nathanshaw/Legatus/PCB/legacy/audio_codec_breakouts/ws8731_audio_codec/panel/ws8731_breakout_panel.brd

## EAGLE design PCB/legacy/audio_codec_breakouts/ws8731_audio_codec/panel/ws8731_breakout_panel.brd (2022-09-17, an earlier design)

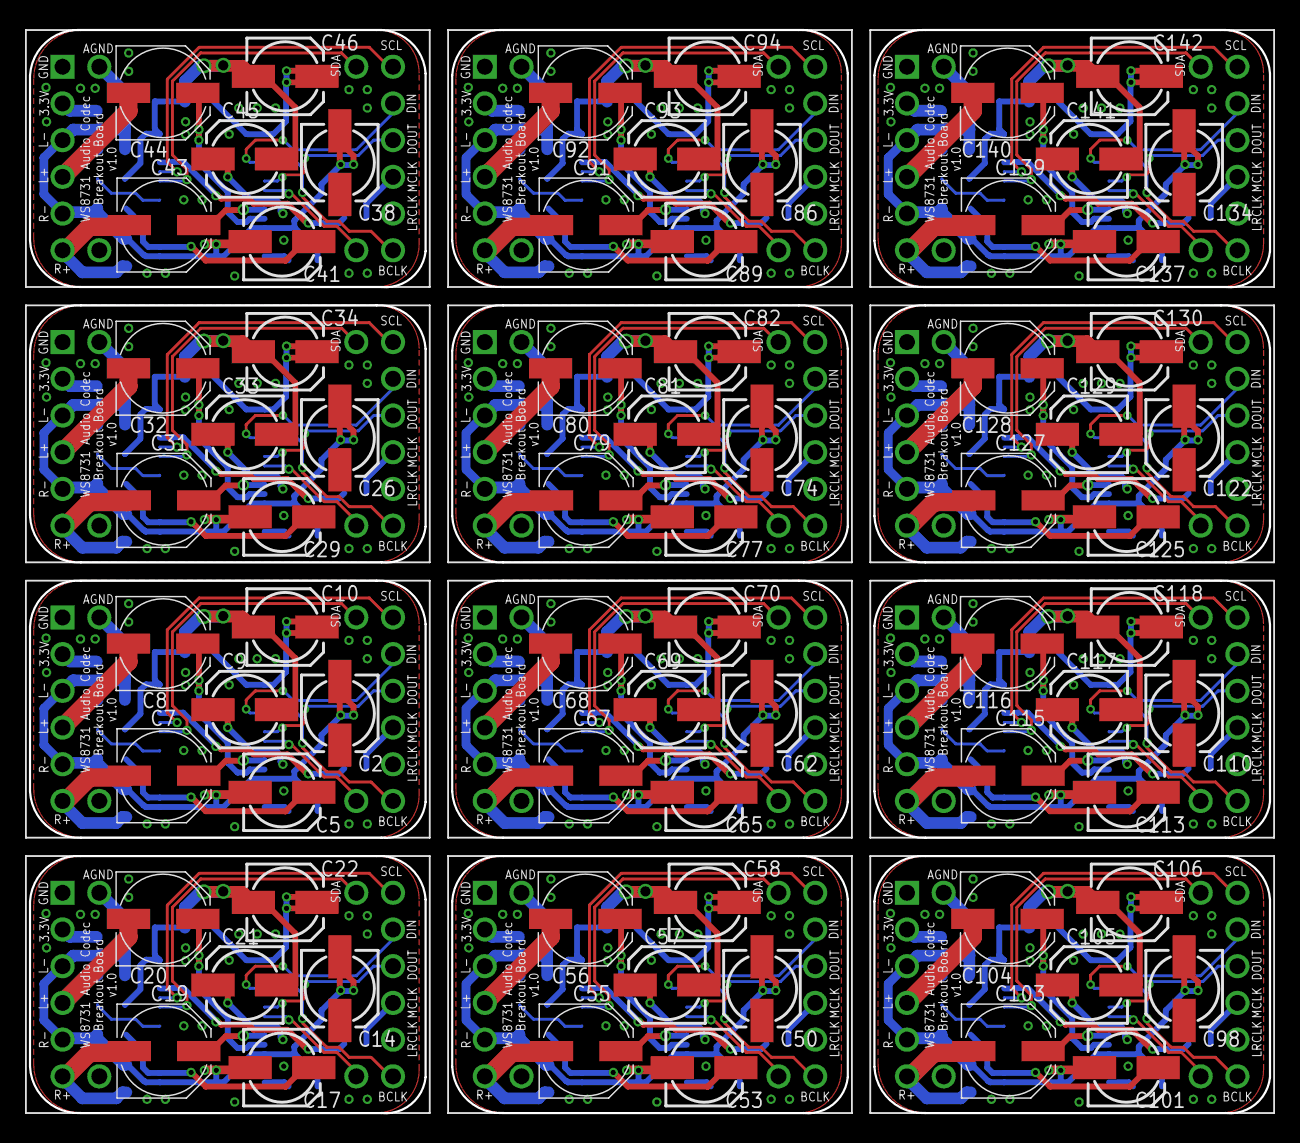
[picture p24: board ws8731_breakout_panel.brd from above]

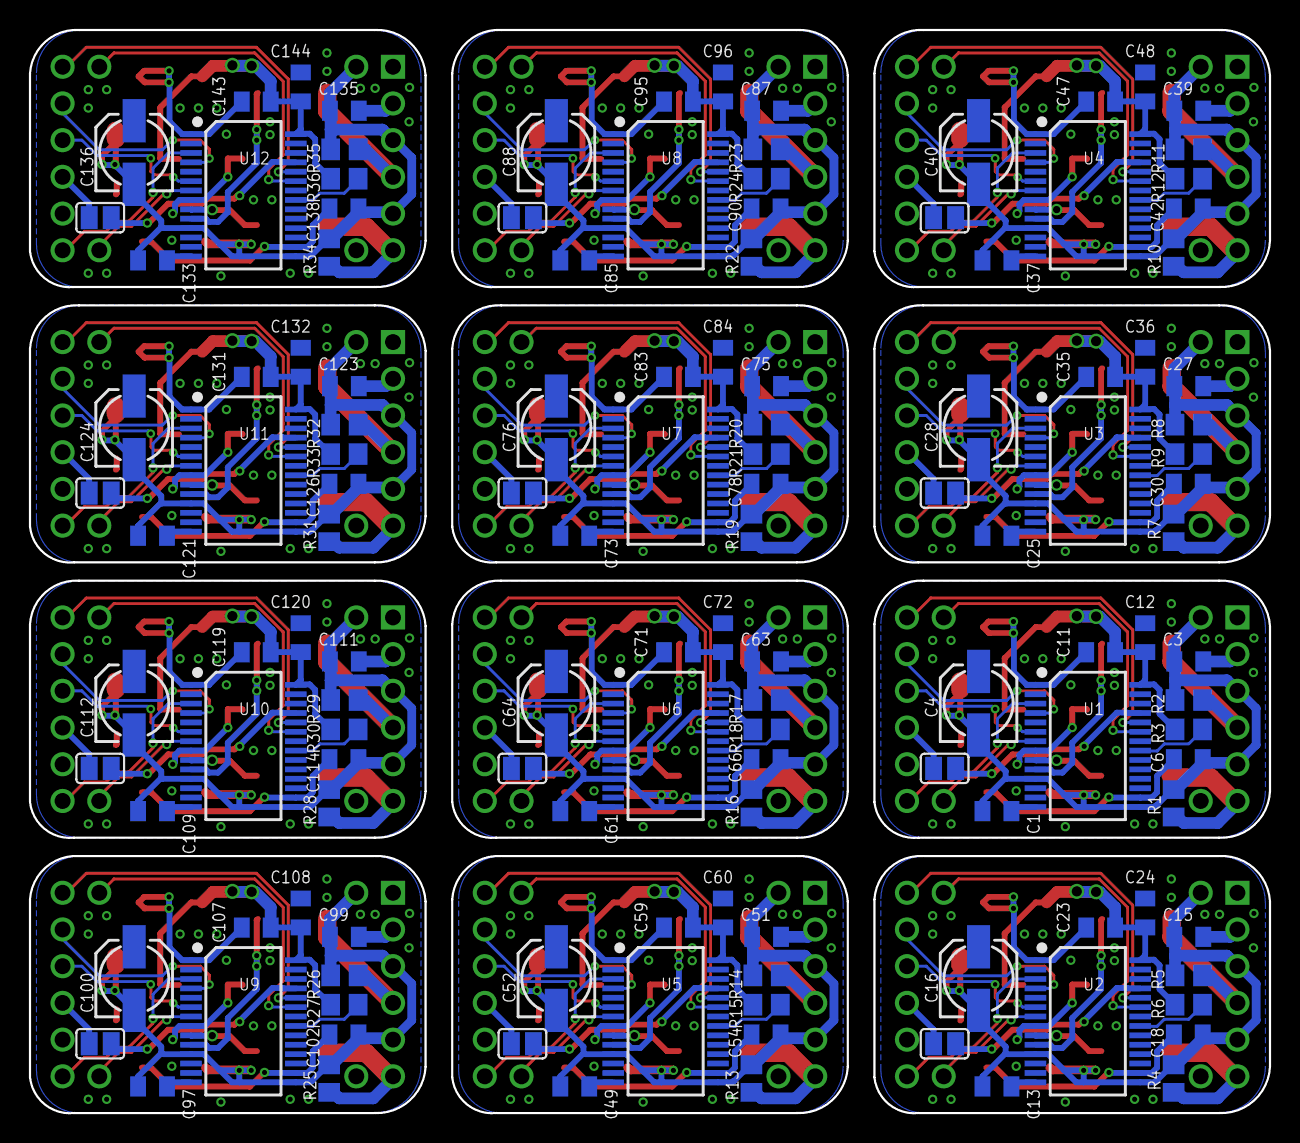
[picture p25: board ws8731_breakout_panel.brd from below]

Board: 2 copper layers, 85.8 x 74.9 mm, 216 parts (132 on the bottom side), 216 nets.

Parts:
C1, C3, C6, C11, C12, C13, C15, C18, C23, C24, C25, C27, C30, C35, C36, C37, C39, C42, C47, C48, C49, C51, C54, C59, C60, C61, C63, C66, C71, C72, C73, C75, C78, C83, C84, C85, C87, C90, C95, C96, C97, C99, C102, C107, C108, C109, C111, C114, C119, C120, C121, C123, C126, C131, C132, C133, C135, C138, C143, C144: 0.1uf; C0805K
C2, C4, C5, C9, C10, C14, C16, C17, C21, C22, C26, C28, C29, C33, C34, C38, C40, C41, C45, C46, C50, C52, C53, C57, C58, C62, C64, C65, C69, C70, C74, C76, C77, C81, C82, C86, C88, C89, C93, C94, C98, C100, C101, C105, C106, C110, C112, C113, C117, C118, C122, C124, C125, C129, C130, C134, C136, C137, C141, C142: 10uf; 153CLV-0505
C7, C8, C19, C20, C31, C32, C43, C44, C55, C56, C67, C68, C79, C80, C91, C92, C103, C104, C115, C116, C127, C128, C139, C140: 220uf; PANASONIC_D
R1, R2, R4, R5, R7, R8, R10, R11, R13, R14, R16, R17, R19, R20, R22, R23, R25, R26, R28, R29, R31, R32, R34, R35: 47k; R0805
R3, R6, R9, R12, R15, R18, R21, R24, R27, R30, R33, R36: 10k; R0805
SJ1, SJ2, SJ3, SJ4, SJ5, SJ6, SJ7, SJ8, SJ9, SJ10, SJ11, SJ12: SJ
U1, U2, U3, U4, U5, U6, U7, U8, U9, U10, U11, U12: CODECODER-WM8731SEDS/V(SSOP28); SSOP28-0.65-10.2X5.2MM
U$1, U$2, U$3, U$4, U$5, U$6, U$7, U$8, U$9, U$10, U$11, U$12: AUDIO_CODEC_BREAKOUT; HSS_CODEC_BREAKOUT

Connections:
3.3V: C13.1, C14.+, C15.1, C16.+, C21.+, C24.1, U2.8, U2.14, U2.27, U$12.3.3
3.3V1: C1.1, C2.+, C3.1, C4.+, C9.+, C12.1, U1.8, U1.14, U1.27, U$1.3.3
3.3V2: C25.1, C26.+, C27.1, C28.+, C33.+, C36.1, U3.8, U3.14, U3.27, U$2.3.3
3.3V3: C37.1, C38.+, C39.1, C40.+, C45.+, C48.1, U4.8, U4.14, U4.27, U$3.3.3
3.3V4: C49.1, C50.+, C51.1, C52.+, C57.+, C60.1, U5.8, U5.14, U5.27, U$4.3.3
3.3V5: C61.1, C62.+, C63.1, C64.+, C69.+, C72.1, U6.8, U6.14, U6.27, U$5.3.3
3.3V6: C73.1, C74.+, C75.1, C76.+, C81.+, C84.1, U7.8, U7.14, U7.27, U$6.3.3
3.3V7: C85.1, C86.+, C87.1, C88.+, C93.+, C96.1, U8.8, U8.14, U8.27, U$7.3.3
3.3V8: C97.1, C98.+, C99.1, C100.+, C105.+, C108.1, U9.8, U9.14, U9.27, U$8.3.3
3.3V9: C109.1, C110.+, C111.1, C112.+, C117.+, C120.1, U10.8, U10.14, U10.27, U$9.3.3
3.3V10: C121.1, C122.+, C123.1, C124.+, C129.+, C132.1, U11.8, U11.14, U11.27, U$10.3.3
3.3V11: C133.1, C134.+, C135.1, C136.+, C141.+, C144.1, U12.8, U12.14, U12.27, U$11.3.3
ADCLRCLK: U2.7, U$12.NA2
ADCLRCLK1: U1.7, U$1.NA2
ADCLRCLK2: U3.7, U$2.NA2
ADCLRCLK3: U4.7, U$3.NA2
ADCLRCLK4: U5.7, U$4.NA2
ADCLRCLK5: U6.7, U$5.NA2
ADCLRCLK6: U7.7, U$6.NA2
ADCLRCLK7: U8.7, U$7.NA2
ADCLRCLK8: U9.7, U$8.NA2
ADCLRCLK9: U10.7, U$9.NA2
ADCLRCLK10: U11.7, U$10.NA2
ADCLRCLK11: U12.7, U$11.NA2
AGND: C13.2, C14.-, C15.2, C16.-, C17.-, C18.2, R4.1, R5.1, U2.11, U2.15, U$12.AGND, U$12.LOUT-, U$12.ROUT-
AGND1: C1.2, C2.-, C3.2, C4.-, C5.-, C6.2, R1.1, R2.1, U1.11, U1.15, U$1.AGND, U$1.LOUT-, U$1.ROUT-
AGND2: C25.2, C26.-, C27.2, C28.-, C29.-, C30.2, R7.1, R8.1, U3.11, U3.15, U$2.AGND, U$2.LOUT-, U$2.ROUT-
AGND3: C37.2, C38.-, C39.2, C40.-, C41.-, C42.2, R10.1, R11.1, U4.11, U4.15, U$3.AGND, U$3.LOUT-, U$3.ROUT-
AGND4: C49.2, C50.-, C51.2, C52.-, C53.-, C54.2, R13.1, R14.1, U5.11, U5.15, U$4.AGND, U$4.LOUT-, U$4.ROUT-
AGND5: C61.2, C62.-, C63.2, C64.-, C65.-, C66.2, R16.1, R17.1, U6.11, U6.15, U$5.AGND, U$5.LOUT-, U$5.ROUT-
AGND6: C73.2, C74.-, C75.2, C76.-, C77.-, C78.2, R19.1, R20.1, U7.11, U7.15, U$6.AGND, U$6.LOUT-, U$6.ROUT-
AGND7: C85.2, C86.-, C87.2, C88.-, C89.-, C90.2, R22.1, R23.1, U8.11, U8.15, U$7.AGND, U$7.LOUT-, U$7.ROUT-
AGND8: C97.2, C98.-, C99.2, C100.-, C101.-, C102.2, R25.1, R26.1, U9.11, U9.15, U$8.AGND, U$8.LOUT-, U$8.ROUT-
AGND9: C109.2, C110.-, C111.2, C112.-, C113.-, C114.2, R28.1, R29.1, U10.11, U10.15, U$9.AGND, U$9.LOUT-, U$9.ROUT-
AGND10: C121.2, C122.-, C123.2, C124.-, C125.-, C126.2, R31.1, R32.1, U11.11, U11.15, U$10.AGND, U$10.LOUT-, U$10.ROUT-
AGND11: C133.2, C134.-, C135.2, C136.-, C137.-, C138.2, R34.1, R35.1, U12.11, U12.15, U$11.AGND, U$11.LOUT-, U$11.ROUT-
BCLK: U2.3, U$12.I2S_BCLK
BCLK1: U1.3, U$1.I2S_BCLK
BCLK2: U3.3, U$2.I2S_BCLK
BCLK3: U4.3, U$3.I2S_BCLK
BCLK4: U5.3, U$4.I2S_BCLK
BCLK5: U6.3, U$5.I2S_BCLK
BCLK6: U7.3, U$6.I2S_BCLK
BCLK7: U8.3, U$7.I2S_BCLK
BCLK8: U9.3, U$8.I2S_BCLK
BCLK9: U10.3, U$9.I2S_BCLK
BCLK10: U11.3, U$10.I2S_BCLK
BCLK11: U12.3, U$11.I2S_BCLK
DBVDD: C22.+, C23.1, U2.1
DBVDD1: C10.+, C11.1, U1.1
DBVDD2: C34.+, C35.1, U3.1
DBVDD3: C46.+, C47.1, U4.1
DBVDD4: C58.+, C59.1, U5.1
DBVDD5: C70.+, C71.1, U6.1
DBVDD6: C82.+, C83.1, U7.1
DBVDD7: C94.+, C95.1, U8.1
DBVDD8: C106.+, C107.1, U9.1
DBVDD9: C118.+, C119.1, U10.1
DBVDD10: C130.+, C131.1, U11.1
DBVDD11: C142.+, C143.1, U12.1
DGND: C21.-, C22.-, C23.2, C24.2, R6.1, U2.28
DGND1: C9.-, C10.-, C11.2, C12.2, R3.1, U1.28
DGND2: C33.-, C34.-, C35.2, C36.2, R9.1, U3.28
DGND3: C45.-, C46.-, C47.2, C48.2, R12.1, U4.28
DGND4: C57.-, C58.-, C59.2, C60.2, R15.1, U5.28
DGND5: C69.-, C70.-, C71.2, C72.2, R18.1, U6.28
DGND6: C81.-, C82.-, C83.2, C84.2, R21.1, U7.28
DGND7: C93.-, C94.-, C95.2, C96.2, R24.1, U8.28
DGND8: C105.-, C106.-, C107.2, C108.2, R27.1, U9.28
DGND9: C117.-, C118.-, C119.2, C120.2, R30.1, U10.28
DGND10: C129.-, C130.-, C131.2, C132.2, R33.1, U11.28
DGND11: C141.-, C142.-, C143.2, C144.2, R36.1, U12.28
DIN: U2.4, U$12.I2S_DIN
DIN1: U1.4, U$1.I2S_DIN
DIN2: U3.4, U$2.I2S_DIN
DIN3: U4.4, U$3.I2S_DIN
DIN4: U5.4, U$4.I2S_DIN
DIN5: U6.4, U$5.I2S_DIN
DIN6: U7.4, U$6.I2S_DIN
DIN7: U8.4, U$7.I2S_DIN
DIN8: U9.4, U$8.I2S_DIN
DIN9: U10.4, U$9.I2S_DIN
DIN10: U11.4, U$10.I2S_DIN
DIN11: U12.4, U$11.I2S_DIN
DOUT: U2.6, U$12.I2S_DOUT
DOUT1: U1.6, U$1.I2S_DOUT
DOUT2: U3.6, U$2.I2S_DOUT
DOUT3: U4.6, U$3.I2S_DOUT
DOUT4: U5.6, U$4.I2S_DOUT
DOUT5: U6.6, U$5.I2S_DOUT
DOUT6: U7.6, U$6.I2S_DOUT
DOUT7: U8.6, U$7.I2S_DOUT
DOUT8: U9.6, U$8.I2S_DOUT
DOUT9: U10.6, U$9.I2S_DOUT
DOUT10: U11.6, U$10.I2S_DOUT
DOUT11: U12.6, U$11.I2S_DOUT
I2S_MCLK: SJ2.2, U$12.I2S_MCLK
I2S_MCLK1: SJ1.2, U$1.I2S_MCLK
I2S_MCLK2: SJ3.2, U$2.I2S_MCLK
I2S_MCLK3: SJ4.2, U$3.I2S_MCLK
I2S_MCLK4: SJ5.2, U$4.I2S_MCLK
I2S_MCLK5: SJ6.2, U$5.I2S_MCLK
I2S_MCLK6: SJ7.2, U$6.I2S_MCLK
I2S_MCLK7: SJ8.2, U$7.I2S_MCLK
I2S_MCLK8: SJ9.2, U$8.I2S_MCLK
I2S_MCLK9: SJ10.2, U$9.I2S_MCLK
I2S_MCLK10: SJ11.2, U$10.I2S_MCLK
I2S_MCLK11: SJ12.2, U$11.I2S_MCLK
LHPOUT: C19.+, U2.9
LHPOUT1: C7.+, U1.9
LHPOUT2: C31.+, U3.9
LHPOUT3: C43.+, U4.9
LHPOUT4: C55.+, U5.9
LHPOUT5: C67.+, U6.9
LHPOUT6: C79.+, U7.9
LHPOUT7: C91.+, U8.9
LHPOUT8: C103.+, U9.9
LHPOUT9: C115.+, U10.9
LHPOUT10: C127.+, U11.9
LHPOUT11: C139.+, U12.9
MCLK: SJ2.1, U2.25
MCLK1: SJ1.1, U1.25
MCLK2: SJ3.1, U3.25
MCLK3: SJ4.1, U4.25
MCLK4: SJ5.1, U5.25
MCLK5: SJ6.1, U6.25
MCLK6: SJ7.1, U7.25
MCLK7: SJ8.1, U8.25
MCLK8: SJ9.1, U9.25
MCLK9: SJ10.1, U10.25
MCLK10: SJ11.1, U11.25
MCLK11: SJ12.1, U12.25
MODE1: R6.2, U2.21
MODE2: R3.2, U1.21
MODE3: R9.2, U3.21
MODE4: R12.2, U4.21
MODE5: R15.2, U5.21
MODE6: R18.2, U6.21
MODE7: R21.2, U7.21
MODE8: R24.2, U8.21
MODE9: R27.2, U9.21
MODE10: R30.2, U10.21
MODE11: R33.2, U11.21
MODE12: R36.2, U12.21
unnamed: C5.+, C6.1, U1.16
unnamed: C17.+, C18.1, U2.16
unnamed: C20.-, R5.2, U$12.LOUT+
unnamed: C19.-, R4.2, U$12.ROUT+
unnamed: C8.-, R2.2, U$1.LOUT+
unnamed: C7.-, R1.2, U$1.ROUT+
unnamed: C29.+, C30.1, U3.16
unnamed: C32.-, R8.2, U$2.LOUT+
unnamed: C31.-, R7.2, U$2.ROUT+
unnamed: C41.+, C42.1, U4.16
unnamed: C44.-, R11.2, U$3.LOUT+
unnamed: C43.-, R10.2, U$3.ROUT+
unnamed: C53.+, C54.1, U5.16
unnamed: C56.-, R14.2, U$4.LOUT+
unnamed: C55.-, R13.2, U$4.ROUT+
unnamed: C65.+, C66.1, U6.16
unnamed: C68.-, R17.2, U$5.LOUT+
unnamed: C67.-, R16.2, U$5.ROUT+
unnamed: C77.+, C78.1, U7.16
unnamed: C80.-, R20.2, U$6.LOUT+
unnamed: C79.-, R19.2, U$6.ROUT+
unnamed: C89.+, C90.1, U8.16
unnamed: C92.-, R23.2, U$7.LOUT+
unnamed: C91.-, R22.2, U$7.ROUT+
unnamed: C101.+, C102.1, U9.16
unnamed: C104.-, R26.2, U$8.LOUT+
unnamed: C103.-, R25.2, U$8.ROUT+
unnamed: C113.+, C114.1, U10.16
unnamed: C116.-, R29.2, U$9.LOUT+
unnamed: C115.-, R28.2, U$9.ROUT+
unnamed: C125.+, C126.1, U11.16
unnamed: C128.-, R32.2, U$10.LOUT+
unnamed: C127.-, R31.2, U$10.ROUT+
unnamed: C137.+, C138.1, U12.16
unnamed: C140.-, R35.2, U$11.LOUT+
unnamed: C139.-, R34.2, U$11.ROUT+
RHPOUT: C20.+, U2.10
RHPOUT1: C8.+, U1.10
RHPOUT2: C32.+, U3.10
RHPOUT3: C44.+, U4.10
RHPOUT4: C56.+, U5.10
RHPOUT5: C68.+, U6.10
RHPOUT6: C80.+, U7.10
RHPOUT7: C92.+, U8.10
RHPOUT8: C104.+, U9.10
RHPOUT9: C116.+, U10.10
RHPOUT10: C128.+, U11.10
RHPOUT11: C140.+, U12.10
SCL: U2.24, U$12.SCL
SCL1: U1.24, U$1.SCL
SCL2: U3.24, U$2.SCL
SCL3: U4.24, U$3.SCL
SCL4: U5.24, U$4.SCL
SCL5: U6.24, U$5.SCL
SCL6: U7.24, U$6.SCL
SCL7: U8.24, U$7.SCL
SCL8: U9.24, U$8.SCL
SCL9: U10.24, U$9.SCL
SCL10: U11.24, U$10.SCL
SCL11: U12.24, U$11.SCL
SDA: U2.23, U$12.SDA
SDA1: U1.23, U$1.SDA
SDA2: U3.23, U$2.SDA
SDA3: U4.23, U$3.SDA
SDA4: U5.23, U$4.SDA
SDA5: U6.23, U$5.SDA
SDA6: U7.23, U$6.SDA
SDA7: U8.23, U$7.SDA
SDA8: U9.23, U$8.SDA
SDA9: U10.23, U$9.SDA
SDA10: U11.23, U$10.SDA
SDA11: U12.23, U$11.SDA
